Linoprit/C64UsbKeyboard/C64UsbKeyboard/include/KeysToHid.h

/*
  This is a derivative of Arduinos Keyboard.h, originally by Peter Barrett
*/

#pragma once

#include "HID.h"
#include "appConfig.h"

// Low level key report: up to 6 keys and shift, ctrl etc at once
typedef struct {
  uint8_t modifiers;
  uint8_t reserved;
  uint8_t keys[6];
} KeyReport;

class KeysToHid {
public:
  KeysToHid(void);
  void reportKeys(RawKeysArray rawKeys, uint8_t scannedKeys);
  void dumpKeyReport();

private:
  KeyReport _keyReport;
  const uint8_t _shiftKeysMask = 0b00110000;

  void sendReport(KeyReport *keys);
  void writeHidToReport(HidKeysArray hidKeys, uint8_t scannedKeys);
  void writeCursorToReport(HidKeysArray hidKeys, uint8_t scannedKeys);

  bool shiftAndCursorActive(HidKeysArray hidKeys, uint8_t scannedKeys);

  uint8_t rawToHid(RawKey rawKey);
  bool addIfModifier(uint8_t hidCode);
  void releaseAll(void);
};
